tbultel/kegcip/bitmaps.h

#pragma once

#define burn_width 56
#define burn_height 64
static unsigned char PROGMEM burn_bits[] = {
   0x00, 0x00, 0x00, 0x00, 0x00, 0x00, 0x00, 0x00, 0x00, 0xf0, 0x00, 0x00,
   0x00, 0x00, 0x00, 0x00, 0xf0, 0x01, 0x00, 0x00, 0x00, 0x00, 0x00, 0xf0,
   0x03, 0x00, 0x00, 0x00, 0x00, 0x00, 0xf0, 0x0f, 0x00, 0x00, 0x00, 0x00,
   0x00, 0xf0, 0x1f, 0x00, 0x00, 0x00, 0x00, 0x00, 0xf0, 0x3f, 0x00, 0x00,
   0x00, 0x00, 0x00, 0xf0, 0x7f, 0x00, 0x00, 0x00, 0x00, 0x00, 0xf0, 0xff,
   0x00, 0x00, 0x00, 0x00, 0x00, 0xf8, 0xff, 0x01, 0x00, 0x00, 0x00, 0x00,
   0xf8, 0xff, 0x03, 0x00, 0x00, 0x00, 0x00, 0xf8, 0xff, 0x07, 0x00, 0x00,
   0x00, 0x00, 0xf8, 0xff, 0x07, 0x00, 0x00, 0x00, 0x00, 0xfc, 0xff, 0x0f,
   0x00, 0x00, 0x00, 0x00, 0xfc, 0xff, 0x1f, 0x00, 0x00, 0x00, 0x00, 0xfc,
   0xff, 0x1f, 0x00, 0x00, 0x00, 0x00, 0xfe, 0xff, 0x3f, 0x00, 0x00, 0x00,
   0x18, 0xfe, 0xff, 0x7f, 0x00, 0x00, 0x00, 0x1c, 0xff, 0xff, 0x7f, 0x00,
   0x00, 0x00, 0x3c, 0xff, 0xff, 0xff, 0x00, 0x00, 0x00, 0x3e, 0xff, 0xff,
   0xff, 0x00, 0x00, 0x00, 0xbe, 0xff, 0xff, 0xff, 0x81, 0x01, 0x00, 0xff,
   0xff, 0xff, 0xff, 0xc1, 0x01, 0x80, 0xff, 0xff, 0xff, 0xff, 0xe1, 0x01,
   0x80, 0xff, 0xff, 0xff, 0xff, 0xe3, 0x03, 0xc0, 0xff, 0xff, 0xff, 0xff,
   0xf3, 0x03, 0xc0, 0xff, 0xff, 0xff, 0xff, 0xf3, 0x03, 0xe0, 0xff, 0xff,
   0xff, 0xff, 0xff, 0x03, 0xe0, 0xff, 0xff, 0xff, 0xff, 0xff, 0x07, 0xf0,
   0xff, 0xff, 0xff, 0xff, 0xff, 0x07, 0xf8, 0xff, 0xff, 0xff, 0xff, 0xff,
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
   0xff, 0xff, 0x7f, 0x00, 0x00, 0x00, 0xc0, 0xff, 0xff, 0x7f, 0x00, 0x00,
   0x00, 0xc0, 0xff, 0xff, 0x7f, 0x00, 0x00, 0x00, 0xc0, 0xff, 0xff, 0x7f,
   0x00, 0x00, 0x00, 0xc0, 0xef, 0xfb, 0x7c, 0x00, 0x00, 0x00, 0x80, 0xc3,
   0x71, 0x38, 0x00, 0x00 };
