tbultel/kegcip/main_menu.h

#pragma once

#include "cycles.h"

extern void main_menu_init();
extern CYCLE_ID main_menu_getid();
extern const char* main_menu_name();
extern void main_menu_disable();
extern void main_menu_enable();
