tbultel/kegcip/cycles.h

#pragma once

#include <stdint.h>
#include "kegcip.h"

typedef enum {
	DESINFECTION,
	RINCAGE_CIRCUIT,
	TRANSFERT,
	LAVAGE,
	CYCLE_COMPLET_FUTS,
#ifdef TEST
	CYCLE_TEST_OUTPUT,
	CYCLE_TEST_THERMO,
	CYCLE_TEST_CIRCU1,
	CYCLE_TEST_CIRCU2,
	CYCLE_TEST_CIRCU3,
	CYCLE_TEST_ENZYMES,
#endif
	CYCLE_VIDE_ACIDE_FUTS,
	CYCLE_VIDE_SOUDE_FUTS,
	CYCLE_VIDE_EAU_FUTS,
	CYCLE_LAST
} CYCLE_ID;

typedef bool (*TRANSITION) (void);
typedef bool (*ACTION) (void);

typedef struct {
	const char* name;
	uint16_t	relays;
	uint32_t	delaySec;	// cycle delay, in seconds. This time is waited before checking transition (where there is one)
	TRANSITION	transition;	// condition to go to next state, in addition to delay
	ACTION		action;		// action done when entering state
} CYCLE_STATE;

extern void cycles_init();

typedef void (*cyclesCallback)(const char *stateName, uint32_t seconds, uint32_t totalSeconds, uint32_t stateDuty);

extern void cycles_set_callback(cyclesCallback cb);

extern const char* cycles_get_name(CYCLE_ID);

extern void cycle_stop();
extern void cycle_resume();
extern void cycle_suspend();
