tbultel/kegcip/rotary_button.h

#pragma once

extern void rotary_button_init();

typedef void (*rotaryCallback)(void);

extern void rotary_register_callbacks(rotaryCallback forward, 
									  rotaryCallback backward,
									  rotaryCallback click);

extern void rotary_tick();

extern void rotary_button_enable();
extern void rotary_button_disable();
